Mauroalfieri/CtrlJ-pen-v2/images/CtrlJ pen v2 motor connector Fusion 360.png

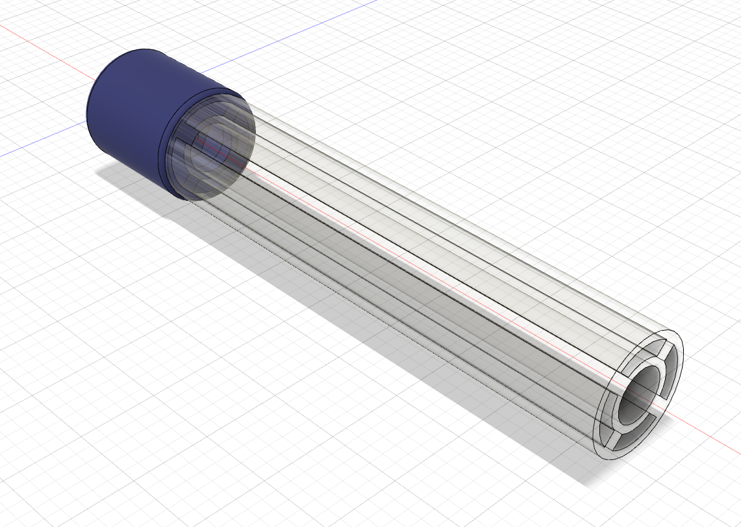
images/CtrlJ pen v2 motor connector Fusion 360.png
